TrojanPinata/Model-K-Pico/PCB/Model K Pico-0.2.kicad_sch

## KiCad design PCB/Model K Pico-0.2.kicad_sch (2022-07-11)

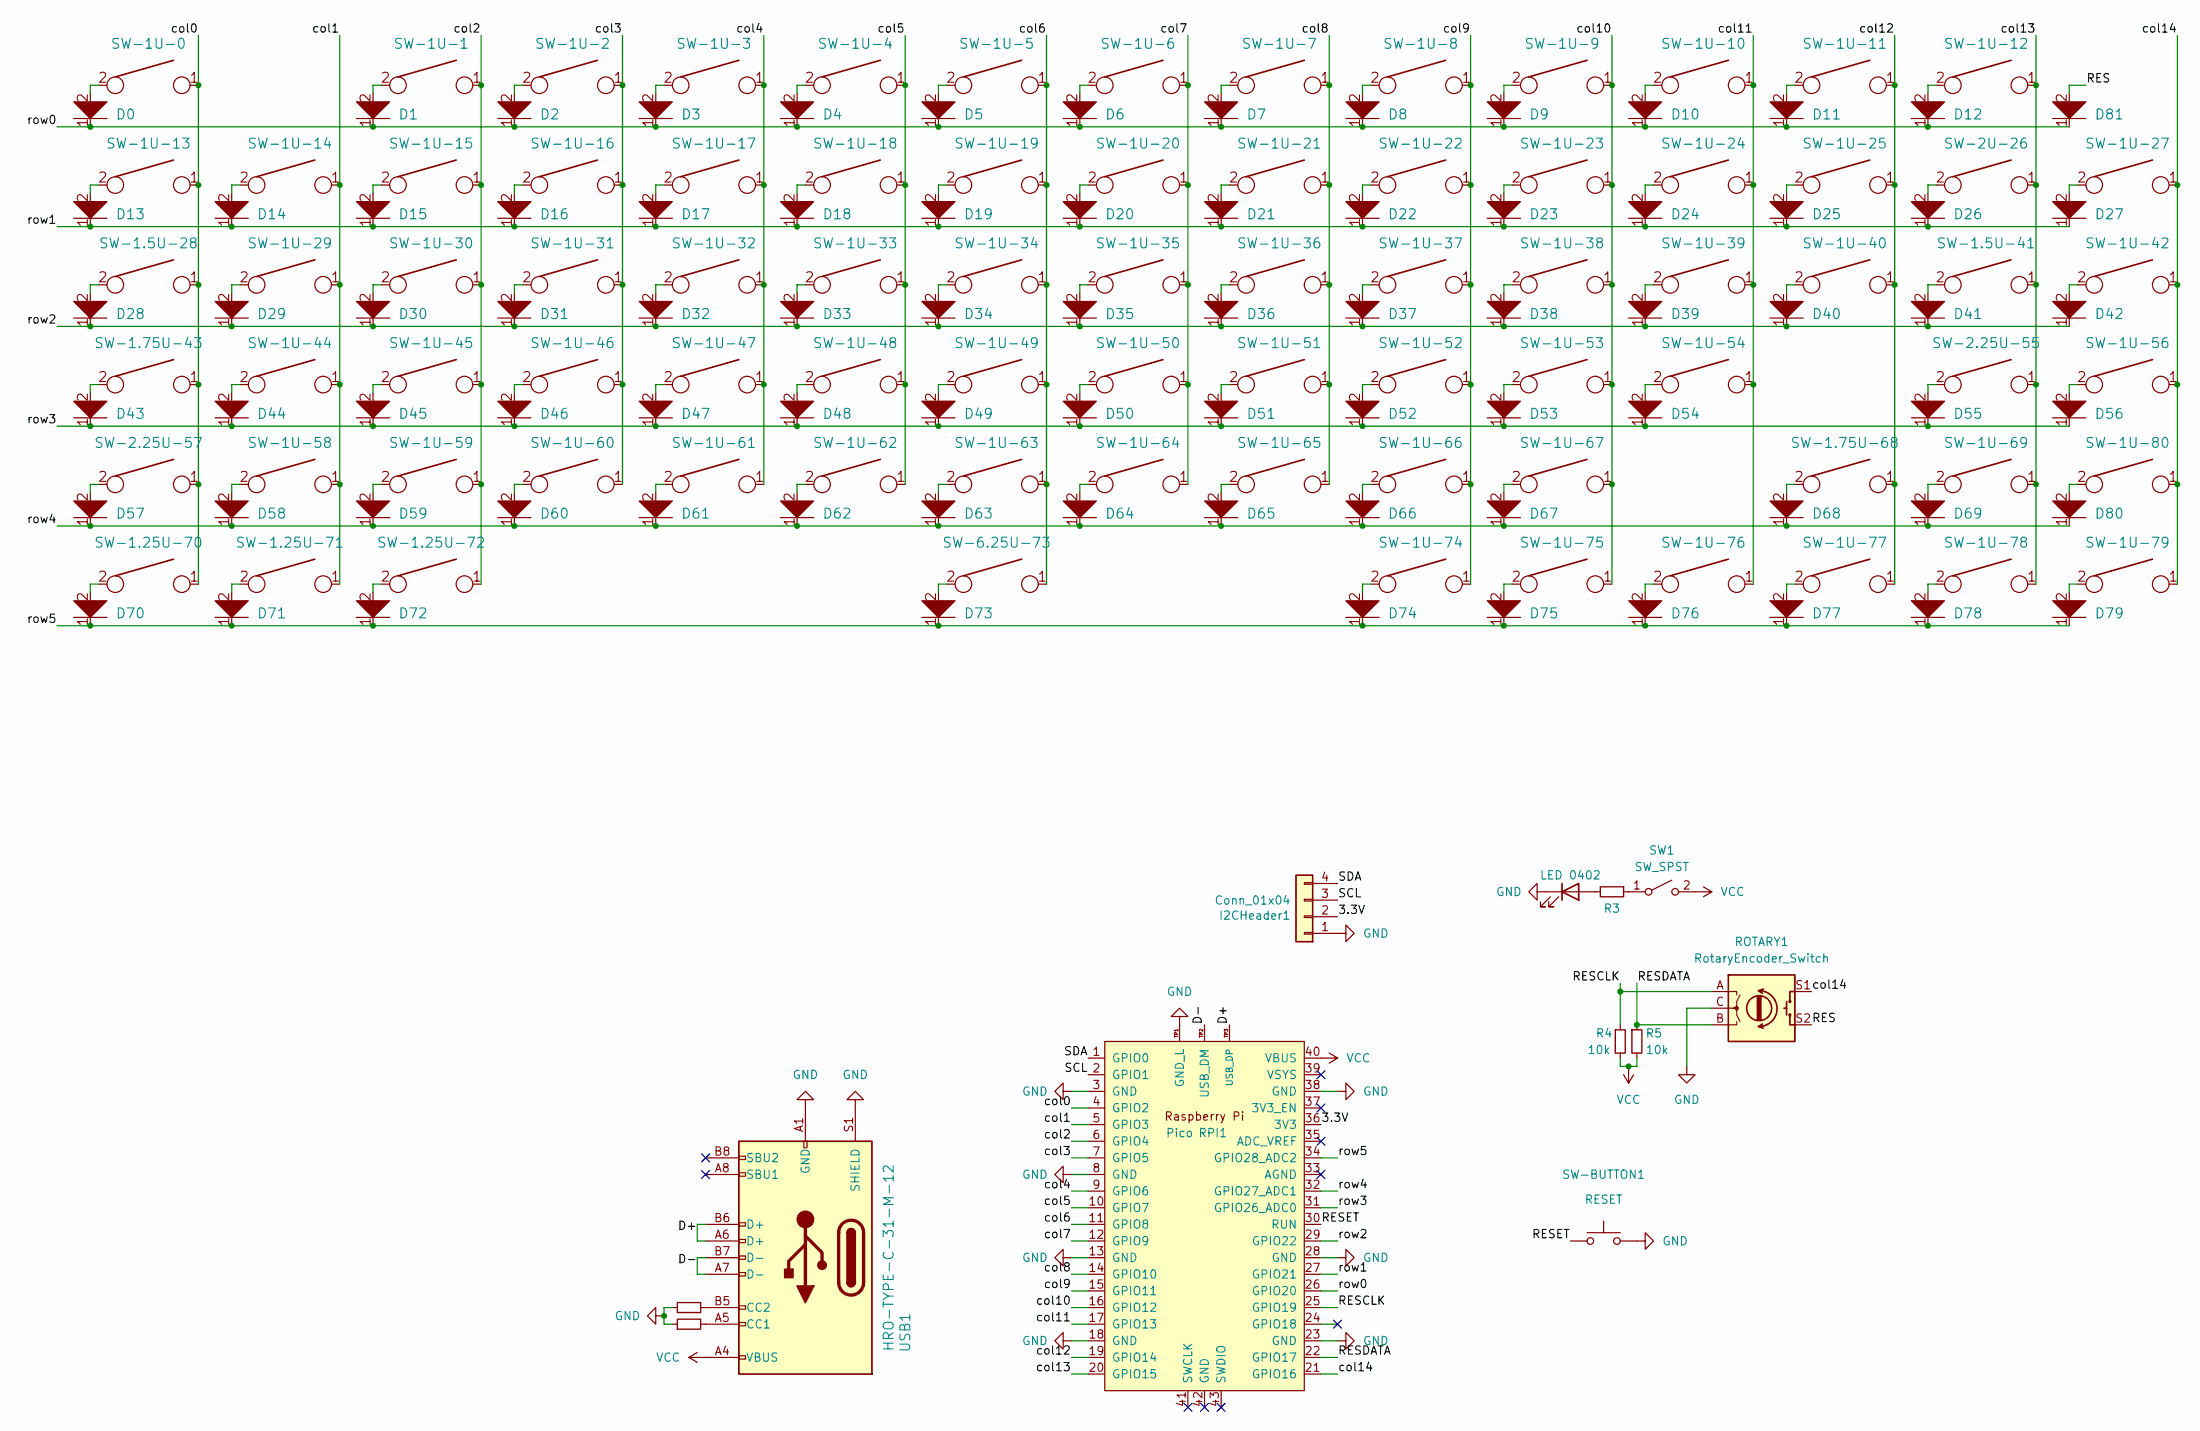
[picture p9: schematic Model K Pico-0.2.kicad_sch]

Parts:
D0, D1, D2, D3, D4, D5, D6, D7, D8, D9, D10, D11, D12, D13, D14, D15, D16, D17, D18, D19, D20, D21, D22, D23, D24, D25, D26, D27, D28, D29, D30, D31, D32, D33, D34, D35, D36, D37, D38, D39, D40, D41, D42, D43, D44, D45, D46, D47, D48, D49, D50, D51, D52, D53, D54, D55, D56, D57, D58, D59, D60, D61, D62, D63, D64, D65, D66, D67, D68, D69, D70, D71, D72, D73, D74, D75, D76, D77, D78, D79, D80, D81: D; D_DO-35_SOD27_P5.08mm_Horizontal
I2CHeader1: Conn_01x04; PinSocket_1x04_P2.54mm_Vertical
PowerLED1: LED 0402; LED_D5.0mm
R1, R2: 5.1k; R_Axial_DIN0204_L3.6mm_D1.6mm_P7.62mm_Horizontal; LCSC C25905
R3: 47K Resistor 0402; R_Axial_DIN0204_L3.6mm_D1.6mm_P7.62mm_Horizontal; LCSC C17513
R4, R5: 10k; R_Axial_DIN0204_L3.6mm_D1.6mm_P7.62mm_Horizontal
ROTARY1: RotaryEncoder_Switch; RotaryEncoder_Alps_EC11E-Switch_Vertical_H20mm_CircularMoun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
RPI1: Pico; RPi_Pico_SMD_TH
SW1: SW_SPST; Omron-B3F-3122-MFG
SW-1.5U-28, SW-1.5U-41: KEYSW; MXOnly-1.5U-NoLED
SW-1.25U-70, SW-1.25U-71, SW-1.25U-72: KEYSW; MXOnly-1.25U-NoLED
SW-1.75U-43, SW-1.75U-68: KEYSW; MXOnly-1.75U-NoLED
SW-1U-0, SW-1U-1, SW-1U-2, SW-1U-3, SW-1U-4, SW-1U-5, SW-1U-6, SW-1U-7, SW-1U-8, SW-1U-9, SW-1U-10, SW-1U-11, SW-1U-12, SW-1U-13, SW-1U-14, SW-1U-15, SW-1U-16, SW-1U-17, SW-1U-18, SW-1U-19, SW-1U-20, SW-1U-21, SW-1U-22, SW-1U-23, SW-1U-24, SW-1U-25, SW-1U-27, SW-1U-29, SW-1U-30, SW-1U-31, SW-1U-32, SW-1U-33, SW-1U-34, SW-1U-35, SW-1U-36, SW-1U-37, SW-1U-38, SW-1U-39, SW-1U-40, SW-1U-42, SW-1U-44, SW-1U-45, SW-1U-46, SW-1U-47, SW-1U-48, SW-1U-49, SW-1U-50, SW-1U-51, SW-1U-52, SW-1U-53, SW-1U-54, SW-1U-56, SW-1U-58, SW-1U-59, SW-1U-60, SW-1U-61, SW-1U-62, SW-1U-63, SW-1U-64, SW-1U-65, SW-1U-66, SW-1U-67, SW-1U-69, SW-1U-74, SW-1U-75, SW-1U-76, SW-1U-77, SW-1U-78, SW-1U-79, SW-1U-80: KEYSW; MXOnly-1U-NoLED
SW-2.25U-55, SW-2.25U-57: KEYSW; MXOnly-2.25U-NoLED
SW-2U-26: KEYSW; MXOnly-2U-NoLED
SW-6.25U-73: KEYSW; MXOnly-6.25U-NoLED
SW-BUTTON1: RESET; Omron-B3F-3122-MFG
USB1: HRO-TYPE-C-31-M-12; USB_C_GCT_USB4085; LCSC C165948

Connections:
3.3V: I2CHeader1.2, RPI1.36 (3V3)
D+: RPI1.TP3 (USB_DP), USB1.A6 (D+), USB1.B6 (D+)
D-: RPI1.TP2 (USB_DM), USB1.A7 (D-), USB1.B7 (D-)
GND: I2CHeader1.1, PowerLED1.1 (K), R1.1, R2.2, ROTARY1.C, RPI1.3 (GND), RPI1.8 (GND), RPI1.13 (GND), RPI1.18 (GND), RPI1.23 (GND), RPI1.28 (GND), RPI1.38 (GND), RPI1.TP1 (GND_L), SW-BUTTON1.2, USB1.A1 (GND), USB1.A12 (GND), USB1.B1 (GND), USB1.B12 (GND), USB1.S1 (SHIELD)
unnamed: D0.2, SW-1U-0.2
unnamed: D1.2, SW-1U-1.2
unnamed: D2.2, SW-1U-2.2
unnamed: D3.2, SW-1U-3.2
unnamed: D4.2, SW-1U-4.2
unnamed: D5.2, SW-1U-5.2
unnamed: D6.2, SW-1U-6.2
unnamed: D7.2, SW-1U-7.2
unnamed: D8.2, SW-1U-8.2
unnamed: D9.2, SW-1U-9.2
unnamed: D10.2, SW-1U-10.2
unnamed: D11.2, SW-1U-11.2
unnamed: D12.2, SW-1U-12.2
unnamed: D13.2, SW-1U-13.2
unnamed: D14.2, SW-1U-14.2
unnamed: D15.2, SW-1U-15.2
unnamed: D16.2, SW-1U-16.2
unnamed: D17.2, SW-1U-17.2
unnamed: D18.2, SW-1U-18.2
unnamed: D19.2, SW-1U-19.2
unnamed: D20.2, SW-1U-20.2
unnamed: D21.2, SW-1U-21.2
unnamed: D22.2, SW-1U-22.2
unnamed: D23.2, SW-1U-23.2
unnamed: D24.2, SW-1U-24.2
unnamed: D25.2, SW-1U-25.2
unnamed: D26.2, SW-2U-26.2
unnamed: D27.2, SW-1U-27.2
unnamed: D28.2, SW-1.5U-28.2
unnamed: D29.2, SW-1U-29.2
unnamed: D30.2, SW-1U-30.2
unnamed: D31.2, SW-1U-31.2
unnamed: D32.2, SW-1U-32.2
unnamed: D33.2, SW-1U-33.2
unnamed: D34.2, SW-1U-34.2
unnamed: D35.2, SW-1U-35.2
unnamed: D36.2, SW-1U-36.2
unnamed: D37.2, SW-1U-37.2
unnamed: D38.2, SW-1U-38.2
unnamed: D39.2, SW-1U-39.2
unnamed: D40.2, SW-1U-40.2
unnamed: D41.2, SW-1.5U-41.2
unnamed: D42.2, SW-1U-42.2
unnamed: D43.2, SW-1.75U-43.2
unnamed: D44.2, SW-1U-44.2
unnamed: D45.2, SW-1U-45.2
unnamed: D46.2, SW-1U-46.2
unnamed: D47.2, SW-1U-47.2
unnamed: D48.2, SW-1U-48.2
unnamed: D49.2, SW-1U-49.2
unnamed: D50.2, SW-1U-50.2
unnamed: D51.2, SW-1U-51.2
unnamed: D52.2, SW-1U-52.2
unnamed: D53.2, SW-1U-53.2
unnamed: D54.2, SW-1U-54.2
unnamed: D55.2, SW-2.25U-55.2
unnamed: D56.2, SW-1U-56.2
unnamed: D57.2, SW-2.25U-57.2
unnamed: D58.2, SW-1U-58.2
unnamed: D59.2, SW-1U-59.2
unnamed: D60.2, SW-1U-60.2
unnamed: D61.2, SW-1U-61.2
unnamed: D62.2, SW-1U-62.2
unnamed: D63.2, SW-1U-63.2
unnamed: D64.2, SW-1U-64.2
unnamed: D65.2, SW-1U-65.2
unnamed: D66.2, SW-1U-66.2
unnamed: D67.2, SW-1U-67.2
unnamed: D68.2, SW-1.75U-68.2
unnamed: D69.2, SW-1U-69.2
unnamed: D70.2, SW-1.25U-70.2
unnamed: D71.2, SW-1.25U-71.2
unnamed: D72.2, SW-1.25U-72.2
unnamed: D73.2, SW-6.25U-73.2
unnamed: D74.2, SW-1U-74.2
unnamed: D75.2, SW-1U-75.2
unnamed: D76.2, SW-1U-76.2
unnamed: D77.2, SW-1U-77.2
unnamed: D78.2, SW-1U-78.2
unnamed: D79.2, SW-1U-79.2
unnamed: D80.2, SW-1U-80.2
unnamed: PowerLED1.2 (A), R3.2
unnamed: R1.2, USB1.A5 (CC1)
unnamed: R2.1, USB1.B5 (CC2)
unnamed: R3.1, SW1.1 (A)
RES: D81.2, ROTARY1.S2
RESCLK: R4.1, ROTARY1.A, RPI1.25 (GPIO19)
RESDATA: R5.1, ROTARY1.B, RPI1.22 (GPIO17)
RESET: RPI1.30 (RUN), SW-BUTTON1.1
SCL: I2CHeader1.3, RPI1.2 (GPIO1)
SDA: I2CHeader1.4, RPI1.1 (GPIO0)
VCC: R4.2, R5.2, RPI1.40 (VBUS), SW1.2 (B), USB1.A4 (VBUS), USB1.A9 (VBUS), USB1.B4 (VBUS), USB1.B9 (VBUS)
col0: RPI1.4 (GPIO2), SW-1.5U-28.1, SW-1.25U-70.1, SW-1.75U-43.1, SW-1U-0.1, SW-1U-13.1, SW-2.25U-57.1
col1: RPI1.5 (GPIO3), SW-1.25U-71.1, SW-1U-14.1, SW-1U-29.1, SW-1U-44.1, SW-1U-58.1
col2: RPI1.6 (GPIO4), SW-1.25U-72.1, SW-1U-1.1, SW-1U-15.1, SW-1U-30.1, SW-1U-45.1, SW-1U-59.1
col3: RPI1.7 (GPIO5), SW-1U-2.1, SW-1U-16.1, SW-1U-31.1, SW-1U-46.1, SW-1U-60.1
col4: RPI1.9 (GPIO6), SW-1U-3.1, SW-1U-17.1, SW-1U-32.1, SW-1U-47.1, SW-1U-61.1
col5: RPI1.10 (GPIO7), SW-1U-4.1, SW-1U-18.1, SW-1U-33.1, SW-1U-48.1, SW-1U-62.1
col6: RPI1.11 (GPIO8), SW-1U-5.1, SW-1U-19.1, SW-1U-34.1, SW-1U-49.1, SW-1U-63.1, SW-6.25U-73.1
col7: RPI1.12 (GPIO9), SW-1U-6.1, SW-1U-20.1, SW-1U-35.1, SW-1U-50.1, SW-1U-64.1
col8: RPI1.14 (GPIO10), SW-1U-7.1, SW-1U-21.1, SW-1U-36.1, SW-1U-51.1, SW-1U-65.1
col9: RPI1.15 (GPIO11), SW-1U-8.1, SW-1U-22.1, SW-1U-37.1, SW-1U-52.1, SW-1U-66.1, SW-1U-74.1
col10: RPI1.16 (GPIO12), SW-1U-9.1, SW-1U-23.1, SW-1U-38.1, SW-1U-53.1, SW-1U-67.1, SW-1U-75.1
col11: RPI1.17 (GPIO13), SW-1U-10.1, SW-1U-24.1, SW-1U-39.1, SW-1U-54.1, SW-1U-76.1
col12: RPI1.19 (GPIO14), SW-1.75U-68.1, SW-1U-11.1, SW-1U-25.1, SW-1U-40.1, SW-1U-77.1
col13: RPI1.20 (GPIO15), SW-1.5U-41.1, SW-1U-12.1, SW-1U-69.1, SW-1U-78.1, SW-2.25U-55.1, SW-2U-26.1
col14: ROTARY1.S1, RPI1.21 (GPIO16), SW-1U-27.1, SW-1U-42.1, SW-1U-56.1, SW-1U-79.1, SW-1U-80.1
row0: D0.1, D1.1, D2.1, D3.1, D4.1, D5.1, D6.1, D7.1, D8.1, D9.1, D10.1, D11.1, D12.1, D81.1, RPI1.26 (GPIO20)
row1: D13.1, D14.1, D15.1, D16.1, D17.1, D18.1, D19.1, D20.1, D21.1, D22.1, D23.1, D24.1, D25.1, D26.1, D27.1, RPI1.27 (GPIO21)
row2: D28.1, D29.1, D30.1, D31.1, D32.1, D33.1, D34.1, D35.1, D36.1, D37.1, D38.1, D39.1, D40.1, D41.1, D42.1, RPI1.29 (GPIO22)
row3: D43.1, D44.1, D45.1, D46.1, D47.1, D48.1, D49.1, D50.1, D51.1, D52.1, D53.1, D54.1, D55.1, D56.1, RPI1.31 (GPIO26_ADC0)
row4: D57.1, D58.1, D59.1, D60.1, D61.1, D62.1, D63.1, D64.1, D65.1, D66.1, D67.1, D68.1, D69.1, D80.1, RPI1.32 (GPIO27_ADC1)
row5: D70.1, D71.1, D72.1, D73.1, D74.1, D75.1, D76.1, D77.1, D78.1, D79.1, RPI1.34 (GPIO28_ADC2)
